tamaroh/maggie44/image/IMG_0104.JPG

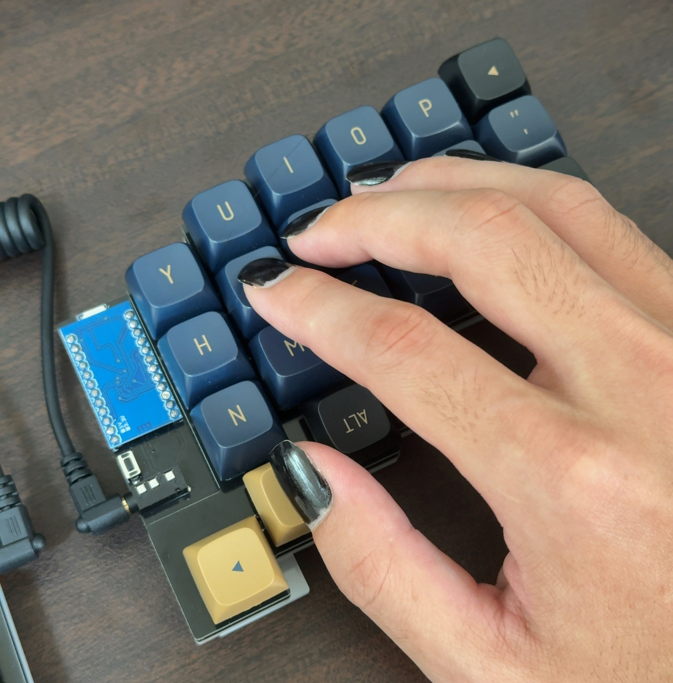
image/IMG_0104.JPG
