tamaroh/maggie44/image/IMG_0105.JPG

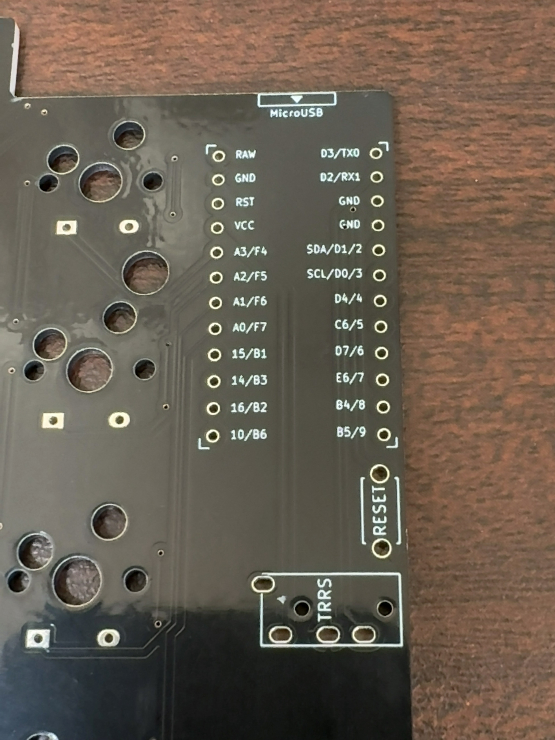
image/IMG_0105.JPG
