tamaroh/maggie44/image/IMG_0114.JPG

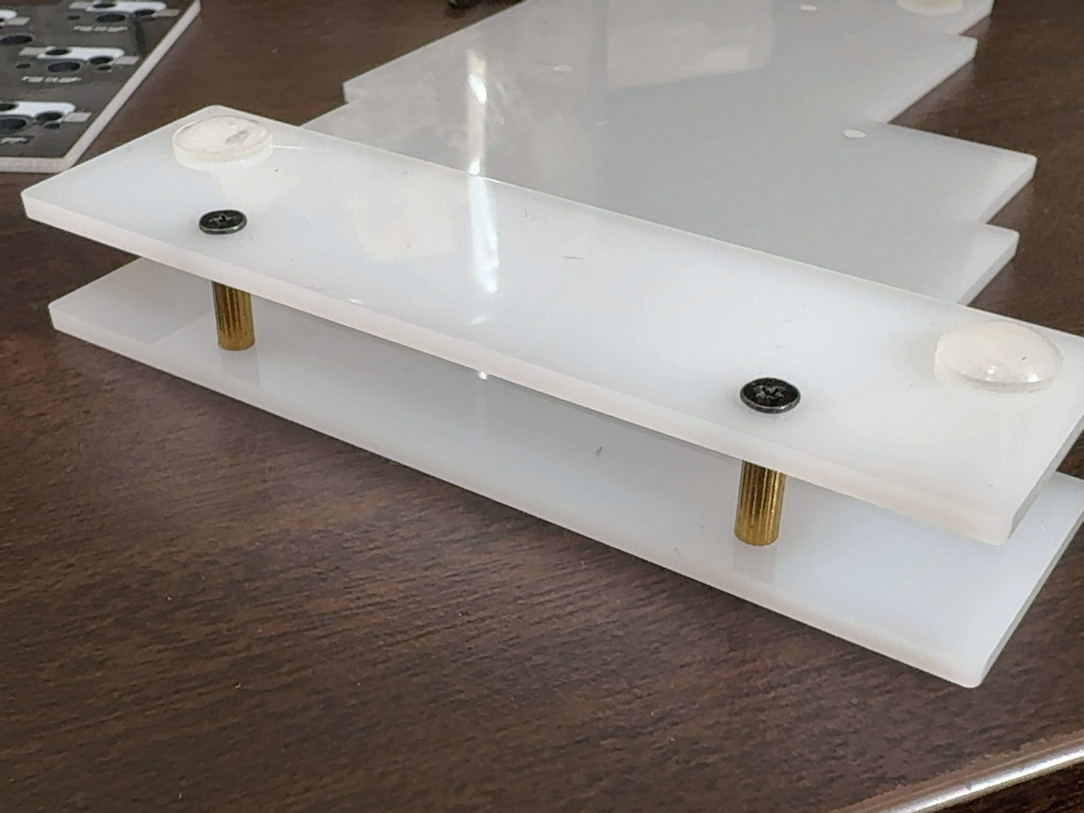
image/IMG_0114.JPG
